jgromes/ESP32-1W-GroundStation/doc/photo2.jpg

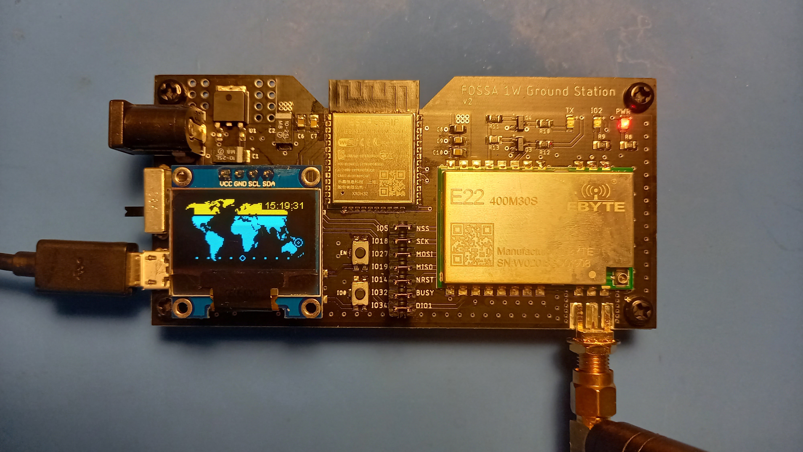
doc/photo2.jpg
